velechit/timelapse/firmware/glyphs.c

#include <stdint.h>
#include "glyphs.h"

const uint8_t timer_glyphs[][39]  = {
{ 0x00, 0x80, 0xf0, 0xf8, 0xfc, 0x3c, 0x1c, 0x3c, 0xfc, 0xf8, 0xf0, 0x80, 0x00, 0x00, 0xff, 0xff, 0xff, 0xff, 0x00, 0x00, 0x00, 0xff, 0xff, 0xff, 0xff, 0x00, 0x00, 0x01, 0x0f, 0x1f, 0x3f, 0x3c, 0x38, 0x3c, 0x3f, 0x1f, 0x0f, 0x01, 0x00 },
{ 0x00, 0x00, 0xc0, 0xe0, 0xf0, 0x78, 0xfc, 0xfc, 0xfc, 0xfc, 0x00, 0x00, 0x00, 0x00, 0x00, 0x00, 0x01, 0x00, 0x00, 0xff, 0xff, 0xff, 0xff, 0x00, 0x00, 0x00, 0x00, 0x00, 0x00, 0x00, 0x00, 0x00, 0x3f, 0x3f, 0x3f, 0x3f, 0x00, 0x00, 0x00 },
{ 0x00, 0x10, 0x38, 0x38, 0x1c, 0x1c, 0x1c, 0x3c, 0xfc, 0xf8, 0xf0, 0x00, 0x00, 0x00, 0x00, 0x00, 0x00, 0xc0, 0xe0, 0xf8, 0xfe, 0x3f, 0x1f, 0x07, 0x00, 0x00, 0x00, 0x38, 0x3e, 0x3f, 0x3f, 0x3b, 0x39, 0x38, 0x38, 0x38, 0x38, 0x38, 0x00 },
{ 0x00, 0x18, 0x38, 0x3c, 0x1c, 0x1c, 0x1c, 0x3c, 0xfc, 0xf8, 0xf0, 0x00, 0x00, 0x00, 0x00, 0x00, 0x1c, 0x1c, 0x1c, 0x1c, 0x3f, 0xff, 0xf3, 0xe1, 0xc0, 0x00, 0x00, 0x1c, 0x38, 0x38, 0x38, 0x38, 0x38, 0x3c, 0x1f, 0x1f, 0x0f, 0x03, 0x00 },
{ 0x00, 0x00, 0x00, 0x00, 0xc0, 0xf0, 0xfc, 0xfc, 0xfc, 0xfc, 0xfc, 0x00, 0x00, 0x80, 0xe0, 0xf8, 0xfe, 0x9f, 0x87, 0x81, 0xff, 0xff, 0xff, 0xff, 0x80, 0x80, 0x03, 0x03, 0x03, 0x03, 0x03, 0x03, 0x03, 0x3f, 0x3f, 0x3f, 0x3f, 0x03, 0x03 },
{ 0x00, 0x00, 0xfc, 0xfc, 0xfc, 0x1c, 0x1c, 0x1c, 0x1c, 0x1c, 0x1c, 0x00, 0x00, 0x00, 0x00, 0x0f, 0x0f, 0x0f, 0x0e, 0x0e, 0x1e, 0xfe, 0xfc, 0xf8, 0xe0, 0x00, 0x00, 0x1c, 0x3c, 0x38, 0x38, 0x38, 0x38, 0x3c, 0x1f, 0x1f, 0x0f, 0x01, 0x00 },
{ 0x00, 0x00, 0xe0, 0xf0, 0xf8, 0x78, 0x3c, 0x1c, 0x1c, 0x1c, 0x1c, 0x00, 0x00, 0x00, 0xff, 0xff, 0xff, 0xf9, 0x0c, 0x0e, 0x0e, 0xfe, 0xfe, 0xfc, 0xf0, 0x00, 0x00, 0x03, 0x0f, 0x1f, 0x3f, 0x3c, 0x38, 0x38, 0x3f, 0x1f, 0x0f, 0x03, 0x00 },
{ 0x00, 0x1c, 0x1c, 0x1c, 0x1c, 0x1c, 0x1c, 0x9c, 0xfc, 0xfc, 0xfc, 0x1c, 0x00, 0x00, 0x00, 0x00, 0x00, 0x00, 0xe0, 0xfc, 0xff, 0x7f, 0x0f, 0x01, 0x00, 0x00, 0x00, 0x00, 0x00, 0x38, 0x3f, 0x3f, 0x1f, 0x03, 0x00, 0x00, 0x00, 0x00, 0x00 },
{ 0x00, 0xe0, 0xf0, 0xf8, 0xfc, 0x1c, 0x1c, 0x1c, 0xfc, 0xf8, 0xf0, 0xc0, 0x00, 0x00, 0xc0, 0xe3, 0xf7, 0xff, 0x3e, 0x1c, 0x3e, 0xff, 0xf7, 0xe3, 0xc0, 0x00, 0x00, 0x07, 0x1f, 0x1f, 0x3f, 0x38, 0x38, 0x38, 0x3f, 0x1f, 0x1f, 0x07, 0x00 },
{ 0x00, 0xe0, 0xf0, 0xf8, 0xfc, 0x1c, 0x1c, 0x3c, 0xfc, 0xf8, 0xf0, 0x80, 0x00, 0x00, 0x0f, 0x3f, 0x7f, 0x7f, 0x70, 0x70, 0x38, 0xff, 0xff, 0xff, 0x7f, 0x00, 0x00, 0x00, 0x38, 0x38, 0x38, 0x38, 0x3c, 0x1e, 0x1f, 0x0f, 0x03, 0x00, 0x00 },
{ 0x00, 0x00, 0x00, 0x00, 0x80, 0x80, 0x80, 0x80, 0x00, 0x00, 0x00, 0x00, 0x00, 0x00, 0x00, 0x00, 0x00, 0x07, 0x07, 0x07, 0x07, 0x00, 0x00, 0x00, 0x00, 0x00, 0x00, 0x00, 0x00, 0x00, 0x3c, 0x3c, 0x3c, 0x3c, 0x00, 0x00, 0x00, 0x00, 0x00 },
};
